KiloanTV/Kiloan-Console/CAD/Sheet Metal (2mm Alu)/Base.step

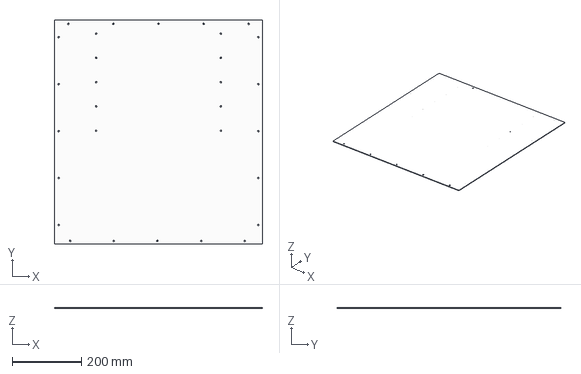
[picture p23: CAD file, 2025-12-08]
CAD/Sheet Metal (2mm Alu)/Base.step
600.0 x 646.9 x 2.00 mm
