KiloanTV/Kiloan-Console/CAD/Sheet Metal (2mm Alu)/Screen-Mount/Screen-Down.step

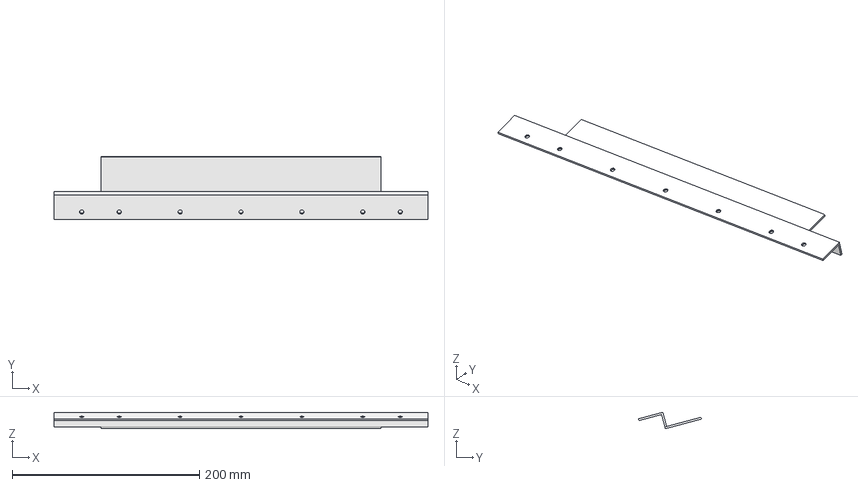
[picture p24: CAD file, 2025-12-03]
CAD/Sheet Metal (2mm Alu)/Screen-Mount/Screen-Down.step
399.2 x 67.4 x 17.6 mm
