KiloanTV/Kiloan-Console/CAD/Sheet Metal (2mm Alu)/made-by-marking.dxf

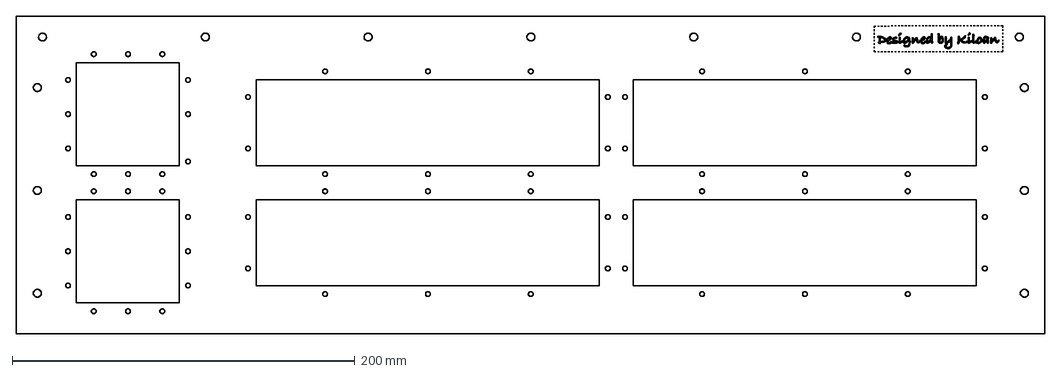
[picture p26: CAD file, 2025-12-08]
CAD/Sheet Metal (2mm Alu)/made-by-marking.dxf
600.0 x 185.0 mm
