KiloanTV/Kiloan-Console/CAD/Sheet Metal (2mm Alu)/Screen-Mount/Screen-up.step

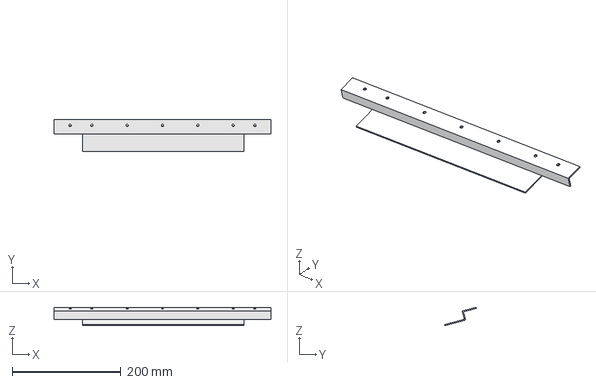
[picture p27: CAD file, 2025-12-03]
CAD/Sheet Metal (2mm Alu)/Screen-Mount/Screen-up.step
399.2 x 59.2 x 33.9 mm
