KiloanTV/Kiloan-Console/CAD/3D Printed/Back Modules/Big-6dnorm.step

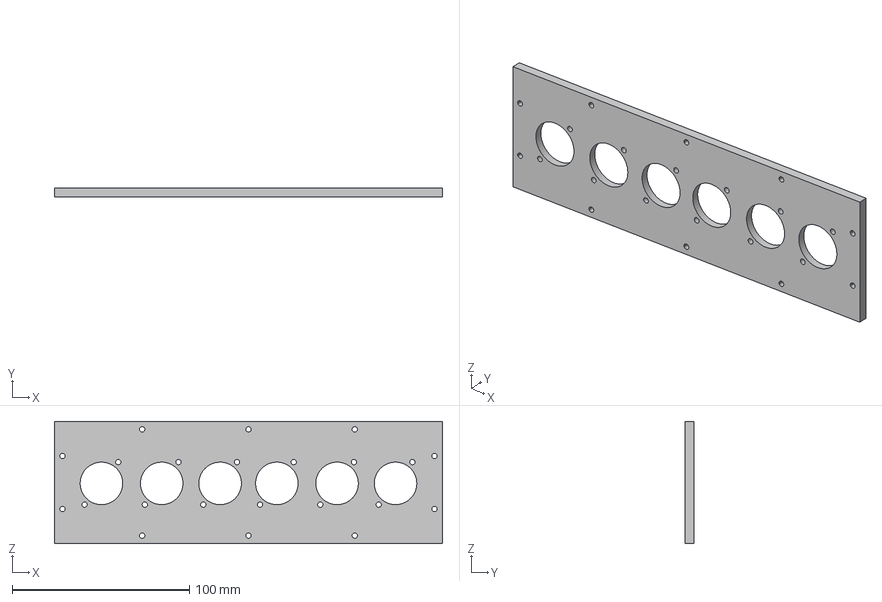
[picture p29: CAD file, 2025-12-03]
CAD/3D Printed/Back Modules/Big-6dnorm.step
219.0 x 5.00 x 69.0 mm
